morlan/NJSlowFeeder/CAD_Models/V1.1/DF Adapters/slowfeed_v1_1_df_54_64_83_ring.stl

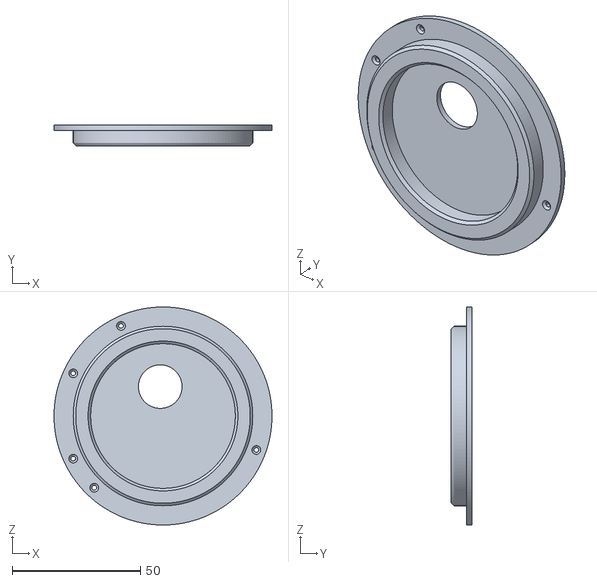
[picture p16: CAD file, 2025-05-04, an earlier design]
CAD_Models/V1.1/DF Adapters/slowfeed_v1_1_df_54_64_83_ring.stl
85.0 x 8.00 x 85.0
